SP5GW/CW_Practice_Tone_Generator/sch/CW_Practice_Tone_Generator.kicad_sch

## KiCad design sch/CW_Practice_Tone_Generator.kicad_sch (2024-10-20)

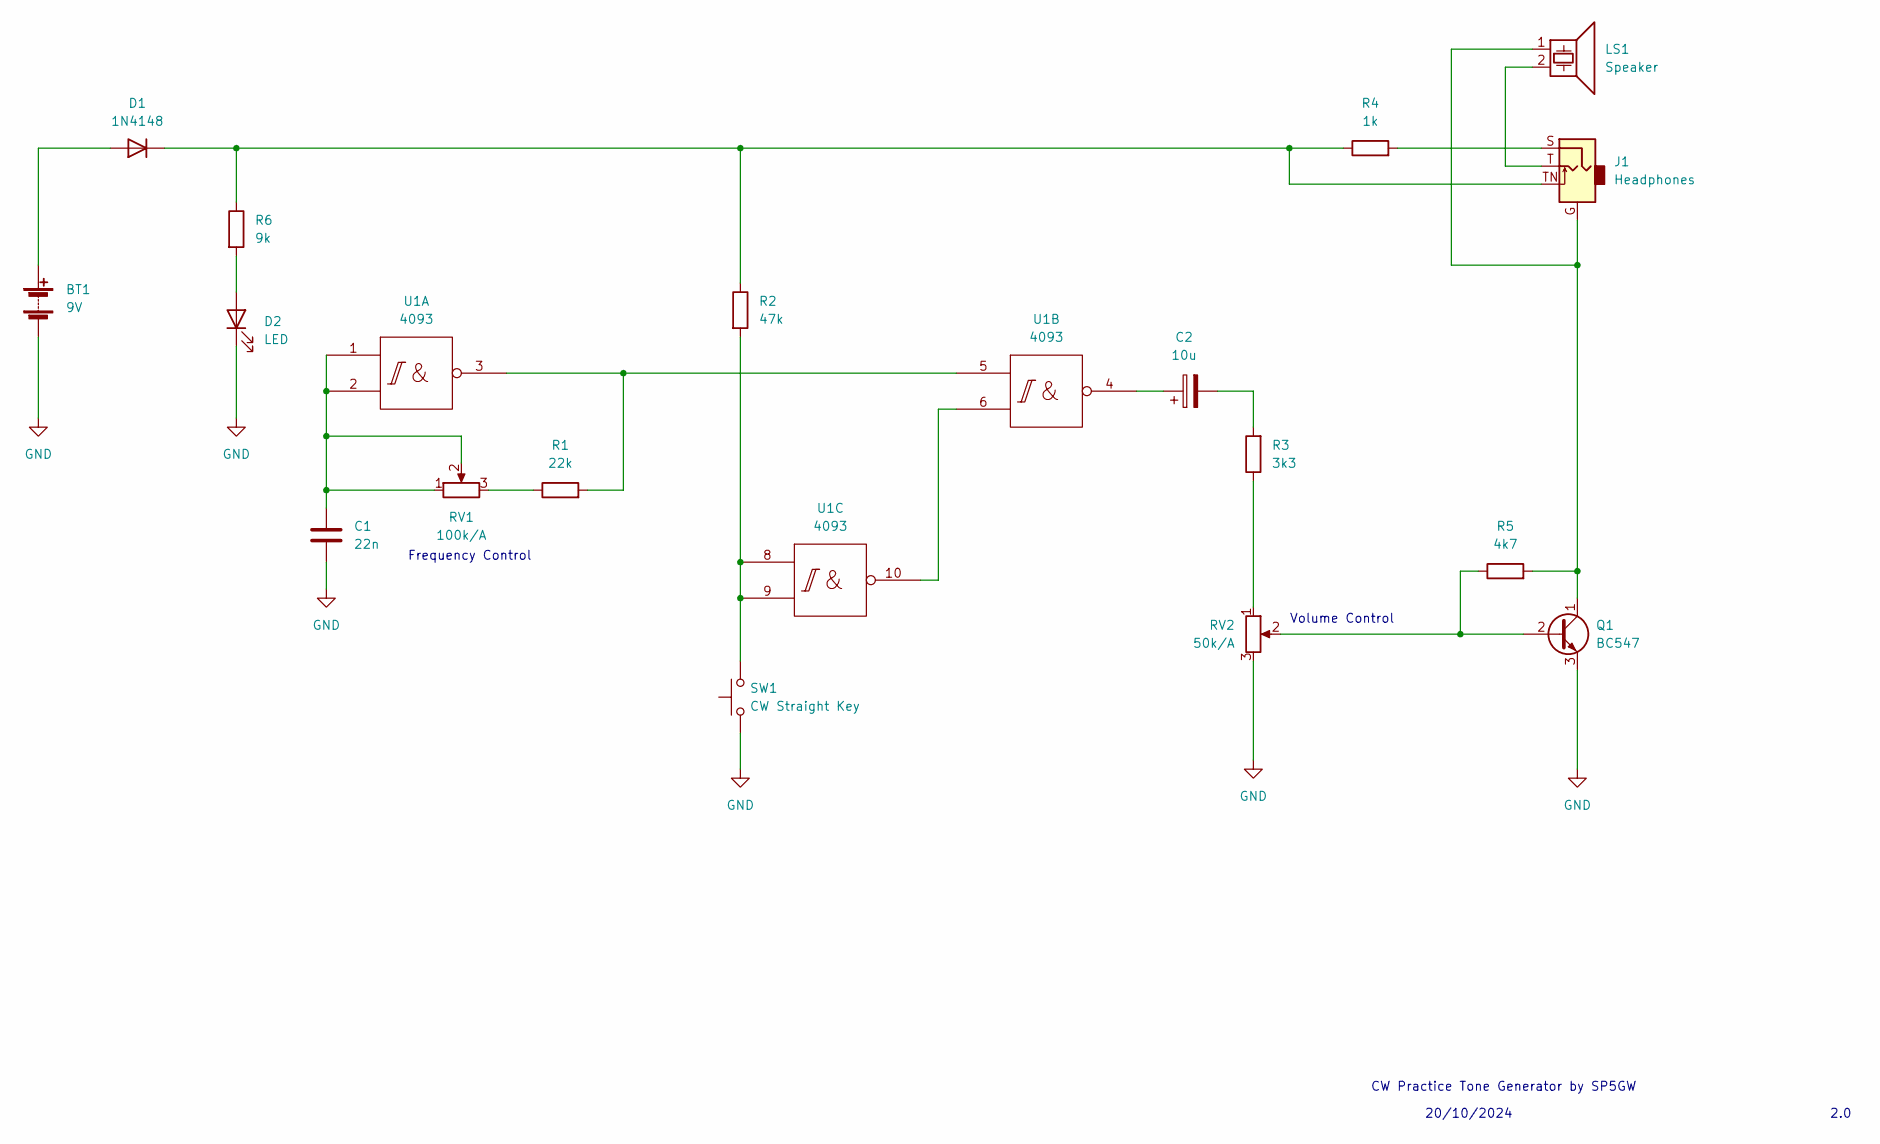
[picture p18: schematic CW_Practice_Tone_Generator.kicad_sch]

Parts:
BT1: 9V
C1: 22n
C2: 10u
D1: 1N4148
D2: LED
J1: Headphones
LS1: Speaker
Q1: BC547; TO-92_Inline
R1: 22k
R2: 47k
R3: 3k3
R4: 1k
R5: 4k7
R6: 9k
RV1: 100k/A
RV2: 50k/A
SW1: CW Straight Key
U1: 4093

Connections:
GND: BT1.2 (-), C1.2, D2.1 (K), Q1.3 (E), RV2.3, SW1.1
unnamed: BT1.1 (+), D1.2 (A)
unnamed: C1.1, RV1.1, RV1.2, U1.1, U1.2
unnamed: C2.1, U1.4
unnamed: C2.2, R3.2
unnamed: D1.1 (K), J1.TN, R2.1, R4.1, R6.1
unnamed: D2.2 (A), R6.2
unnamed: J1.G, LS1.1, Q1.1 (C), R5.2
unnamed: J1.S, R4.2
unnamed: J1.T, LS1.2
unnamed: Q1.2 (B), R5.1, RV2.2
unnamed: R1.1, RV1.3
unnamed: R1.2, U1.3, U1.5
unnamed: R2.2, SW1.2, U1.8, U1.9
unnamed: R3.1, RV2.1
unnamed: U1.6, U1.10

Notes on the sheet:
Frequency Control
CW Practice Tone Generator by SP5GW
Volume Control
2.0
20/10/2024
